Christophe45/ESP32-Lorawan/kicad lora node/lora node esp32.jpg

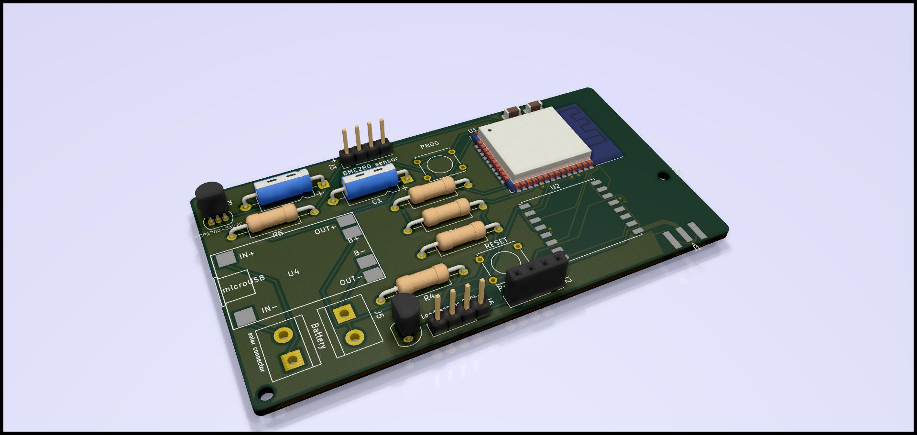
kicad lora node/lora node esp32.jpg
