Christophe45/ESP32-Lorawan/pictures/image0.jpeg

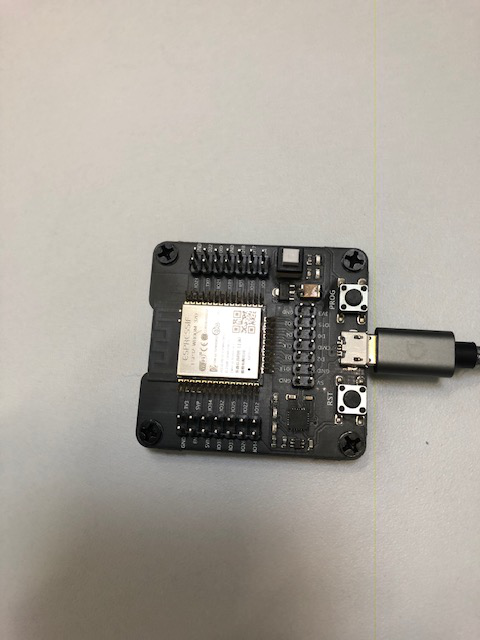
pictures/image0.jpeg
