Christophe45/ESP32-Lorawan/pictures/lorawan1.jpg

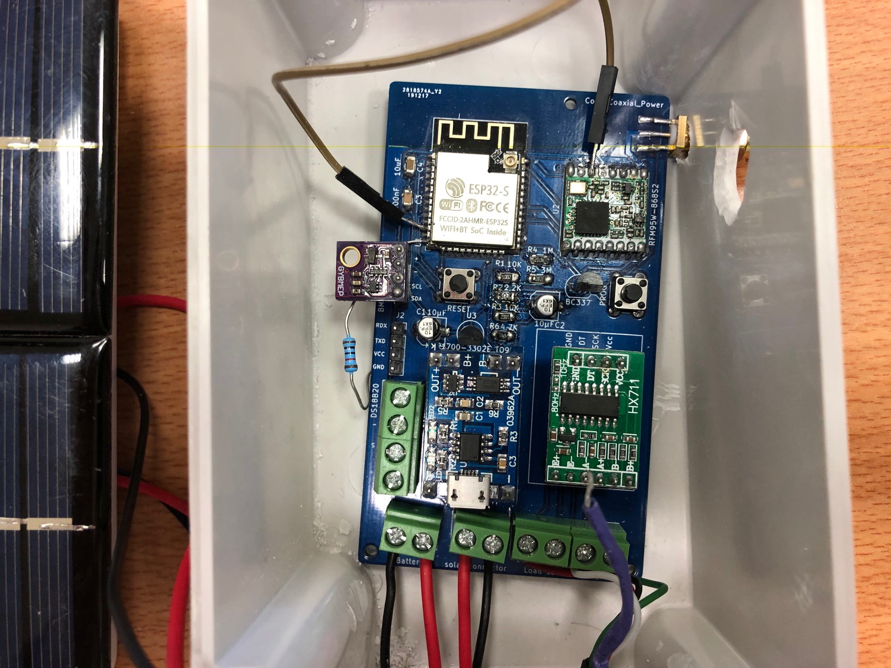
pictures/lorawan1.jpg
