Christophe45/ESP32-Lorawan/pictures/lorawan.jpg

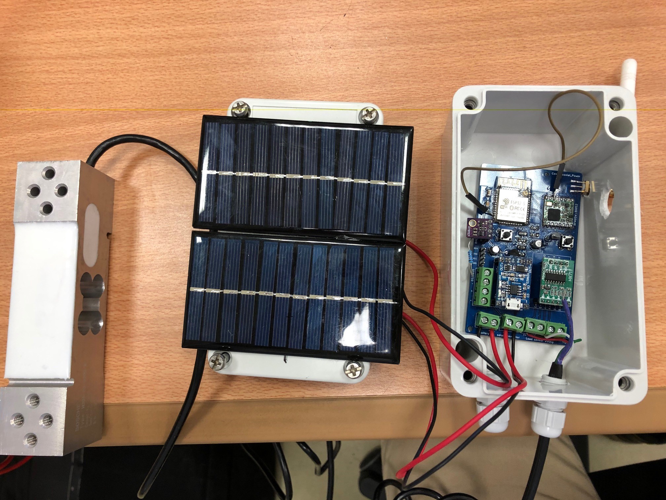
pictures/lorawan.jpg
