Christophe45/ESP32-Lorawan/pictures/schema.JPG

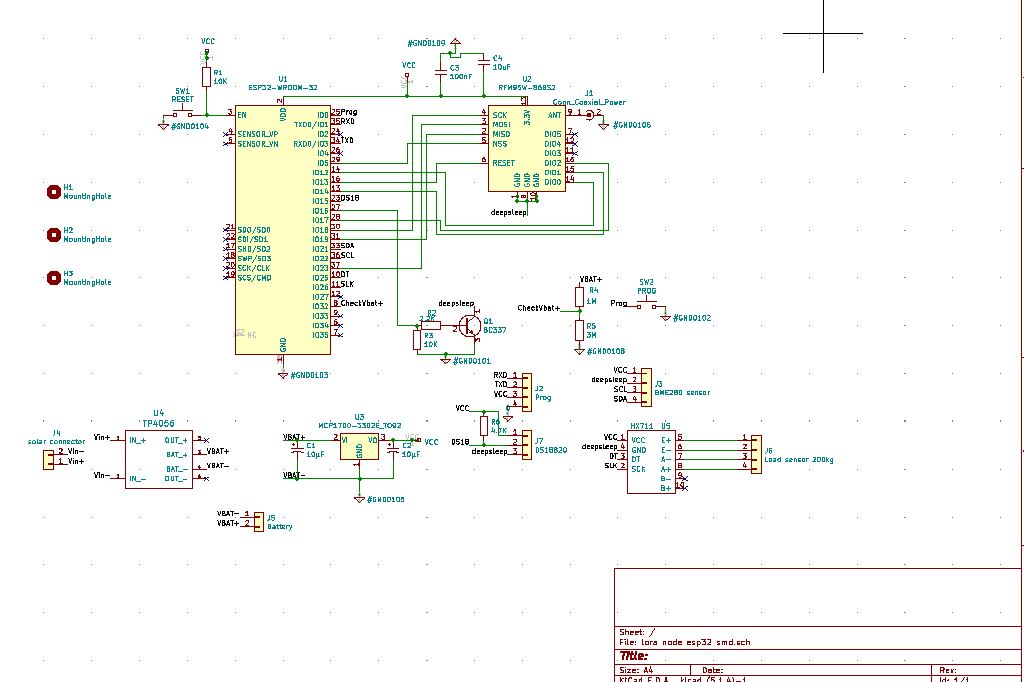
pictures/schema.JPG
